tordex/trackball/main/paw3395/paw3395.cpp

#include "driver/spi_master.h"
#include "driver/gpio.h"
#include "driver/rtc_io.h"
#include <esp_private/esp_clk.h>
#include "esp_log.h"
#include "paw3395.h"

// Timing constants
const uint8_t PAW3395_TIMINGS_SRAD     = 2; // 2μs
const uint8_t PAW3395_TIMINGS_SRWSRR   = 2; // 2μs
const uint8_t PAW3395_TIMINGS_SWW      = 5; // 5μs
const uint8_t PAW3395_TIMINGS_SWR      = 5; // 5μs
const uint8_t PAW3395_TIMINGS_NCS_SCLK = 1; // 120ns
const uint8_t PAW3395_TIMINGS_BEXIT    = 4; // 500ns

const uint8_t PAW3395_SPI_WRITE = 0x80;

// Register addresses
const uint8_t PAW3395_REG_MOTION            = 0x02;
const uint8_t PAW3395_REG_DELTA_X_L         = 0x03;
const uint8_t PAW3395_REG_DELTA_X_H         = 0x04;
const uint8_t PAW3395_REG_DELTA_Y_L         = 0x05;
const uint8_t PAW3395_REG_DELTA_Y_H         = 0x06;
const uint8_t PAW3395_REG_MOTION_BURST      = 0x16;
const uint8_t PAW3395_REG_POWERUPRESET      = 0x3A;
const uint8_t PAW3395_REG_SET_RESOLUTION    = 0x47;
const uint8_t PAW3395_REG_RESOLUTION_X_LOW  = 0x48;
const uint8_t PAW3395_REG_RESOLUTION_X_HIGH = 0x49;
const uint8_t PAW3395_REG_RESOLUTION_Y_LOW  = 0x4A;
const uint8_t PAW3395_REG_RESOLUTION_Y_HIGH = 0x4B;
const uint8_t PAW3395_REG_RIPPLE_CONTROL    = 0x5A;
const uint8_t PAW3395_REG_MOTION_CTRL       = 0x5C;

// Register values
const uint8_t PAW3395_POWERUPRESET_POWERON = 0x5A;

// Register bits
const uint8_t PAW3395_OP_MODE0 = 0;
const uint8_t PAW3395_OP_MODE1 = 1;
const uint8_t PAW3395_PG_FIRST = 6;
const uint8_t PAW3395_PG_VALID = 7;

esp_err_t paw3395::init(spi_host_device_t host_id, gpio_num_t ncs_pin, gpio_num_t pin_motion,
                        const OnMotionCallback_t& on_motion)
{
    const uint8_t PAW3395_INVALID_PRODUCT_ID_0 = 0x00;
    const uint8_t PAW3395_INVALID_PRODUCT_ID_1 = 0xFF;
    const int     PAW3395_INIT_RETRIES         = 3;

    m_pin_ncs            = ncs_pin;
    m_pin_motion         = pin_motion;
    m_on_motion_callback = on_motion;

    // Configure NCS pin
    gpio_config_t io_conf = {};
    io_conf.pin_bit_mask  = (1ULL << m_pin_ncs);
    io_conf.mode          = GPIO_MODE_OUTPUT;
    io_conf.pull_up_en    = GPIO_PULLUP_DISABLE;
    io_conf.pull_down_en  = GPIO_PULLDOWN_DISABLE;
    io_conf.intr_type     = GPIO_INTR_DISABLE;
    gpio_config(&io_conf);

    cs_high();

    // Configure SPI device
    spi_device_interface_config_t devcfg = {};
    devcfg.clock_speed_hz                = 10000000; // 10MHz
    devcfg.mode                          = 3;        // SPI Mode 3 (CPOL=1, CPHA=1)
    devcfg.spics_io_num                  = -1;       // Manually control CS
    devcfg.queue_size                    = 7;

    esp_err_t ret = spi_bus_add_device(host_id, &devcfg, &m_spi);
    if(ret != ESP_OK)
    {
        ESP_LOGE(m_log_tag, "SPI device add failed: %d\n", ret);
        return ret;
    }

    cs_high();
    uint8_t product_id     = 0;
    uint8_t inv_product_id = 0;
    bool    init_ok        = false;
    for(int attempt = 1; attempt <= PAW3395_INIT_RETRIES; ++attempt)
    {
        Power_up_sequence();
        product_id     = read_register(0x00);
        inv_product_id = read_register(0x5F);

        if(product_id != PAW3395_INVALID_PRODUCT_ID_0 && product_id != PAW3395_INVALID_PRODUCT_ID_1 &&
           (product_id ^ inv_product_id) == 0xFF)
        {
            init_ok = true;
            break;
        }

        ESP_LOGW(m_log_tag, "Invalid Product ID 0x%02X/0x%02X (attempt %d/%d)", product_id, inv_product_id, attempt,
                 PAW3395_INIT_RETRIES);
        delay_ms(10);
    }

    if(!init_ok)
    {
        ESP_LOGE(m_log_tag, "PAW3395 init failed, invalid Product ID after retries: 0x%02X/0x%02X", product_id,
                 inv_product_id);
        return ESP_ERR_INVALID_RESPONSE;
    }

    ESP_LOGI(m_log_tag, "PAW3395 Product ID: 0x%02X", product_id);

    // Enable RIPPLE CONTROL
    write_register(PAW3395_REG_RIPPLE_CONTROL, 0x90);

    // Lift cut 2mm
    set_lift_cut(2);

    // Read and clear any pending motion data before starting normal operation.
    motion_burst_data data;
    for(int i = 0; i < 5; i++)
    {
        motion_burst(&data);
        vTaskDelay(pdMS_TO_TICKS(1));
    }

    ret = init_motion_pin();
    if(ret != ESP_OK)
    {
        ESP_LOGE(m_log_tag, "Failed to initialize motion pin");
        return ret;
    }

    // If MOTION is already low, no negedge will occur. Trigger one read cycle now.
    if(gpio_get_level(m_pin_motion) == 0)
    {
        ESP_LOGE(m_log_tag, "MOTION pin is already low");
    }

    if(xTaskCreate((TaskFunction_t) motion_task, "paw3395_motion", 4096, this, 5, &m_motion_task) != pdPASS)
    {
        ESP_LOGE(m_log_tag, "Failed to create motion task");
        return ESP_FAIL;
    }

    return ESP_OK;
}

void paw3395::set_lift_cut(uint8_t lift_height)
{
    write_register(0x7F, 0xC0);
    write_register(0x4E, lift_height);
    write_register(0x7F, 0x00);
}

static void IRAM_ATTR motion_isr_handler(void* arg)
{
    BaseType_t woken = pdFALSE;
    auto       sem   = static_cast<SemaphoreHandle_t>(arg);
    xSemaphoreGiveFromISR(sem, &woken);
    portYIELD_FROM_ISR(woken);
}

esp_err_t paw3395::init_motion_pin()
{
    if(!m_motion_semaphore)
    {
        m_motion_semaphore = xSemaphoreCreateBinary();
        if(!m_motion_semaphore)
        {
            ESP_LOGE(m_log_tag, "Failed to create semaphore");
            return ESP_FAIL;
        }
    }

    if(rtc_gpio_is_valid_gpio(m_pin_motion))
    {
        // When waking from deep sleep, wakeup pins can stay in RTC mode.
        // Release it so edge interrupts work in digital GPIO mode.
        rtc_gpio_deinit(m_pin_motion);
    }

    const gpio_config_t io_conf = {
        .pin_bit_mask = (1ULL << m_pin_motion),
        .mode         = GPIO_MODE_INPUT,
        .pull_up_en   = GPIO_PULLUP_ENABLE,
        .pull_down_en = GPIO_PULLDOWN_DISABLE,
        .intr_type    = GPIO_INTR_NEGEDGE,
    };
    esp_err_t ret = gpio_config(&io_conf);
    if(ret != ESP_OK)
    {
        ESP_LOGE(m_log_tag, "Motion pin gpio_config failed: %d", ret);
        return ret;
    }

    gpio_isr_handler_remove(m_pin_motion);

    ret = gpio_isr_handler_add(m_pin_motion, motion_isr_handler, m_motion_semaphore);
    if(ret != ESP_OK)
    {
        ESP_LOGE(m_log_tag, "gpio_isr_handler_add failed: %d", ret);
        return ret;
    }

    ret = gpio_intr_enable(m_pin_motion);
    if(ret != ESP_OK)
    {
        ESP_LOGE(m_log_tag, "gpio_intr_enable failed: %d", ret);
        return ret;
    }

    return ESP_OK;
}

void paw3395::stop_motion_task()
{
    m_stop = true;
    vTaskDelay(pdMS_TO_TICKS(7)); // Give some time for the motion task to exit
    gpio_intr_disable(m_pin_motion);
    gpio_isr_handler_remove(m_pin_motion);
}

void paw3395::motion_task(void* param)
{
    auto pThis = static_cast<paw3395*>(param);
    while(!pThis->m_stop)
    {
        if(pThis->m_motion_semaphore && xSemaphoreTake(pThis->m_motion_semaphore, pdMS_TO_TICKS(5)))
        {
            int16_t dx      = 0;
            int16_t dy      = 0;
            int     counter = 0;
            while(counter < 5)
            {
                if(pThis->read_motion_burst(&dx, &dy))
                {
                    if(pThis->m_on_motion_callback)
                    {
                        pThis->m_on_motion_callback(dx, dy);
                    }
                } else
                {
                    counter++;
                    vTaskDelay(pdMS_TO_TICKS(1));
                }
            }
        }
    }
    vTaskDelete(NULL);
}

void paw3395::delay_125_ns(uint8_t nns)
{
    uint32_t cpu_freq_hz = esp_clk_cpu_freq();
    uint32_t cycles      = (125 * nns) / (1000000000 / cpu_freq_hz);
    uint32_t start       = esp_cpu_get_cycle_count();
    while(esp_cpu_get_cycle_count() - start < cycles)
        ;
}

uint8_t paw3395::SPI_SendReceive(uint8_t data)
{
    spi_transaction_t t = {};
    t.length            = 8;
    t.tx_buffer         = &data;
    t.rxlength          = 8;
    t.rx_buffer         = &data;

    esp_err_t ret = spi_device_polling_transmit(m_spi, &t);
    if(ret != ESP_OK)
    {
        printf("SPI transaction failed: %d\n", ret);
    }
    return data;
}

uint8_t paw3395::read_register(uint8_t address, bool apply_cs)
{
    if(apply_cs)
    {
        cs_low();
    }
    delay_125_ns(1);
    SPI_SendReceive(address);
    delay_us(5); // t_SRAD
    uint8_t temp = SPI_SendReceive(0xFF);
    if(apply_cs)
    {
        cs_high();
    }
    delay_us(5); // t_SWW
    return temp;
}

void paw3395::write_register(uint8_t address, uint8_t value)
{
    cs_low();
    delay_125_ns(1);
    SPI_SendReceive(address | 0x80);
    SPI_SendReceive(value);
    cs_high();
    delay_us(5); // t_SWW
}

void paw3395::Power_up_sequence()
{
    uint8_t reg_it;
    delay_ms(60);
    cs_low();
    delay_125_ns(PAW3395_TIMINGS_NCS_SCLK);
    cs_high();
    delay_125_ns(PAW3395_TIMINGS_NCS_SCLK);
    cs_low();
    delay_125_ns(PAW3395_TIMINGS_NCS_SCLK);

    write_register(PAW3395_REG_POWERUPRESET, PAW3395_POWERUPRESET_POWERON);
    delay_ms(10);
    Power_Up_Initializaton_Register_Setting();
    cs_high();
    delay_125_ns(PAW3395_TIMINGS_NCS_SCLK);

    for(reg_it = 0x02; reg_it <= 0x06; reg_it++)
    {
        read_register(reg_it);
        delay_us(PAW3395_TIMINGS_SRWSRR);
    }
    cs_high();
    delay_125_ns(PAW3395_TIMINGS_BEXIT);
}

bool paw3395::read_motion(int16_t* dx, int16_t* dy)
{
    uint8_t motion, x_l, x_h, y_l, y_h;

    // Read the Motion register. This will freeze the Delta_X and Delta_Y registers until they are read.
    motion = read_register(PAW3395_REG_MOTION);
    if((motion & 0x80) != 0)
    {
        cs_low();
        x_l = read_register(PAW3395_REG_DELTA_X_L, false);
        x_h = read_register(PAW3395_REG_DELTA_X_H, false);
        y_l = read_register(PAW3395_REG_DELTA_Y_L, false);
        y_h = read_register(PAW3395_REG_DELTA_Y_H, false);
        cs_high();

        *dx = (int16_t) (x_l | (x_h << 8));
        *dy = (int16_t) (y_l | (y_h << 8));
        return *dx != 0 || *dy != 0;
    }
    *dx = 0;
    *dy = 0;
    return false;
}

bool paw3395::read_motion_burst(int16_t* dx, int16_t* dy)
{
    motion_burst_data burst = {};
    motion_burst(&burst);
    if((burst.motion & 0x80) != 0)
    {
        *dx = (int16_t) (burst.delta_x_l | (burst.delta_x_h << 8));
        *dy = (int16_t) (burst.delta_y_l | (burst.delta_y_h << 8));
        return *dx != 0 || *dy != 0;
    }
    *dx = 0;
    *dy = 0;
    return false;
}

void paw3395::motion_burst(motion_burst_data* values)
{
    uint8_t* buffer = reinterpret_cast<uint8_t*>(values);
    cs_low();
    delay_125_ns(PAW3395_TIMINGS_NCS_SCLK);
    SPI_SendReceive(PAW3395_REG_MOTION_BURST);
    delay_us(PAW3395_TIMINGS_SRAD);
    for(uint8_t i = 0; i < 12; i++)
    {
        buffer[i] = SPI_SendReceive(0x00);
    }
    cs_high();
    delay_125_ns(PAW3395_TIMINGS_BEXIT);
}

void paw3395::Power_Up_Initializaton_Register_Setting()
{
    uint8_t read_tmp;
    uint8_t i;
    write_register(0x7F, 0x07);
    write_register(0x40, 0x41);
    write_register(0x7F, 0x00);
    write_register(0x40, 0x80);
    write_register(0x7F, 0x0E);
    write_register(0x55, 0x0D);
    write_register(0x56, 0x1B);
    write_register(0x57, 0xE8);
    write_register(0x58, 0xD5);
    write_register(0x7F, 0x14);
    write_register(0x42, 0xBC);
    write_register(0x43, 0x74);
    write_register(0x4B, 0x20);
    write_register(0x4D, 0x00);
    write_register(0x53, 0x0E);
    write_register(0x7F, 0x05);
    write_register(0x44, 0x04);
    write_register(0x4D, 0x06);
    write_register(0x51, 0x40);
    write_register(0x53, 0x40);
    write_register(0x55, 0xCA);
    write_register(0x5A, 0xE8);
    write_register(0x5B, 0xEA);
    write_register(0x61, 0x31);
    write_register(0x62, 0x64);
    write_register(0x6D, 0xB8);
    write_register(0x6E, 0x0F);

    write_register(0x70, 0x02);
    write_register(0x4A, 0x2A);
    write_register(0x60, 0x26);
    write_register(0x7F, 0x06);
    write_register(0x6D, 0x70);
    write_register(0x6E, 0x60);
    write_register(0x6F, 0x04);
    write_register(0x53, 0x02);
    write_register(0x55, 0x11);
    write_register(0x7A, 0x01);
    write_register(0x7D, 0x51);
    write_register(0x7F, 0x07);
    write_register(0x41, 0x10);
    write_register(0x42, 0x32);
    write_register(0x43, 0x00);
    write_register(0x7F, 0x08);
    write_register(0x71, 0x4F);
    write_register(0x7F, 0x09);
    write_register(0x62, 0x1F);
    write_register(0x63, 0x1F);
    write_register(0x65, 0x03);
    write_register(0x66, 0x03);
    write_register(0x67, 0x1F);
    write_register(0x68, 0x1F);
    write_register(0x69, 0x03);
    write_register(0x6A, 0x03);
    write_register(0x6C, 0x1F);

    write_register(0x6D, 0x1F);
    write_register(0x51, 0x04);
    write_register(0x53, 0x20);
    write_register(0x54, 0x20);
    write_register(0x71, 0x0C);
    write_register(0x72, 0x07);
    write_register(0x73, 0x07);
    write_register(0x7F, 0x0A);
    write_register(0x4A, 0x14);
    write_register(0x4C, 0x14);
    write_register(0x55, 0x19);
    write_register(0x7F, 0x14);
    write_register(0x4B, 0x30);
    write_register(0x4C, 0x03);
    write_register(0x61, 0x0B);
    write_register(0x62, 0x0A);
    write_register(0x63, 0x02);
    write_register(0x7F, 0x15);
    write_register(0x4C, 0x02);
    write_register(0x56, 0x02);
    write_register(0x41, 0x91);
    write_register(0x4D, 0x0A);
    write_register(0x7F, 0x0C);
    write_register(0x4A, 0x10);
    write_register(0x4B, 0x0C);
    write_register(0x4C, 0x40);
    write_register(0x41, 0x25);
    write_register(0x55, 0x18);
    write_register(0x56, 0x14);
    write_register(0x49, 0x0A);
    write_register(0x42, 0x00);
    write_register(0x43, 0x2D);
    write_register(0x44, 0x0C);
    write_register(0x54, 0x1A);
    write_register(0x5A, 0x0D);
    write_register(0x5F, 0x1E);
    write_register(0x5B, 0x05);
    write_register(0x5E, 0x0F);
    write_register(0x7F, 0x0D);
    write_register(0x48, 0xDD);
    write_register(0x4F, 0x03);
    write_register(0x52, 0x49);

    write_register(0x51, 0x00);
    write_register(0x54, 0x5B);
    write_register(0x53, 0x00);

    write_register(0x56, 0x64);
    write_register(0x55, 0x00);
    write_register(0x58, 0xA5);
    write_register(0x57, 0x02);
    write_register(0x5A, 0x29);
    write_register(0x5B, 0x47);
    write_register(0x5C, 0x81);
    write_register(0x5D, 0x40);
    write_register(0x71, 0xDC);
    write_register(0x70, 0x07);
    write_register(0x73, 0x00);
    write_register(0x72, 0x08);
    write_register(0x75, 0xDC);
    write_register(0x74, 0x07);
    write_register(0x77, 0x00);
    write_register(0x76, 0x08);
    write_register(0x7F, 0x10);
    write_register(0x4C, 0xD0);
    write_register(0x7F, 0x00);
    write_register(0x4F, 0x63);
    write_register(0x4E, 0x00);
    write_register(0x52, 0x63);
    write_register(0x51, 0x00);
    write_register(0x54, 0x54);
    write_register(0x5A, 0x10);
    write_register(0x77, 0x4F);
    write_register(0x47, 0x01);
    write_register(0x5B, 0x40);
    write_register(0x64, 0x60);
    write_register(0x65, 0x06);
    write_register(0x66, 0x13);
    write_register(0x67, 0x0F);
    write_register(0x78, 0x01);
    write_register(0x79, 0x9C);
    write_register(0x40, 0x00);
    write_register(0x55, 0x02);
    write_register(0x23, 0x70);
    write_register(0x22, 0x01);

    delay_ms(1);

    for(i = 0; i < 60; i++)
    {
        read_tmp = read_register(0x6C);
        if(read_tmp == 0x80)
        {
            break;
        }
        delay_ms(1);
    }
    if(i == 60)
    {
        write_register(0x7F, 0x14);
        write_register(0x6C, 0x00);
        write_register(0x7F, 0x00);
    }
    write_register(0x22, 0x00);
    write_register(0x55, 0x00);
    write_register(0x7F, 0x07);
    write_register(0x40, 0x40);
    write_register(0x7F, 0x00);
}

void paw3395::set_dpi(uint16_t CPI_Num)
{
    uint8_t temp;
    write_register(PAW3395_REG_MOTION_CTRL, 0x00);
    temp = (uint8_t) (((CPI_Num / 50) << 8) >> 8);
    write_register(PAW3395_REG_RESOLUTION_X_LOW, temp);
    temp = (uint8_t) ((CPI_Num / 50) >> 8);
    write_register(PAW3395_REG_RESOLUTION_X_HIGH, temp);
    write_register(PAW3395_REG_SET_RESOLUTION, 0x01);
}

void paw3395::office_mode()
{
    write_register(0x7F, 0x05);
    write_register(0x51, 0x28);
    write_register(0x53, 0x30);
    write_register(0x61, 0x3B);
    write_register(0x6E, 0x1F);
    write_register(0x7F, 0x07);
    write_register(0x42, 0x32);
    write_register(0x43, 0x00);
    write_register(0x7F, 0x0D);
    write_register(0x51, 0x00);
    write_register(0x52, 0x49);
    write_register(0x53, 0x00);
    write_register(0x54, 0x5B);
    write_register(0x55, 0x00);
    write_register(0x56, 0x64);
    write_register(0x57, 0x02);
    write_register(0x58, 0xA5);
    write_register(0x7F, 0x00);
    write_register(0x54, 0x52);
    write_register(0x78, 0x0A);
    write_register(0x79, 0x0F);
    uint8_t tmp = read_register(0x40);
    tmp         = (tmp & 0xFC) | 0x02;
    write_register(0x40, tmp);
}

void paw3395::gaming_mode()
{
    write_register(0x7F, 0x05);
    write_register(0x51, 0x40);
    write_register(0x53, 0x40);
    write_register(0x61, 0x31);
    write_register(0x6E, 0x0F);
    write_register(0x7F, 0x07);
    write_register(0x42, 0x2F);
    write_register(0x43, 0x00);
    write_register(0x7F, 0x0D);
    write_register(0x51, 0x12);
    write_register(0x52, 0xDB);
    write_register(0x53, 0x12);
    write_register(0x54, 0xDC);
    write_register(0x55, 0x12);
    write_register(0x56, 0xEA);
    write_register(0x57, 0x15);
    write_register(0x58, 0x2D);
    write_register(0x7F, 0x00);
    write_register(0x54, 0x55);
    write_register(0x40, 0x83);
}

void paw3395::low_power_mode()
{
    write_register(0x7F, 0x05);
    write_register(0x51, 0x40);
    write_register(0x53, 0x40);
    write_register(0x61, 0x3B);
    write_register(0x6E, 0x1F);
    write_register(0x7F, 0x07);
    write_register(0x42, 0x32);
    write_register(0x43, 0x00);
    write_register(0x7F, 0x0D);
    write_register(0x51, 0x00);
    write_register(0x52, 0x49);
    write_register(0x53, 0x00);
    write_register(0x54, 0x5B);
    write_register(0x55, 0x00);
    write_register(0x56, 0x64);
    write_register(0x57, 0x02);
    write_register(0x58, 0xA5);
    write_register(0x7F, 0x00);
    write_register(0x54, 0x54);
    write_register(0x78, 0x01);
    write_register(0x79, 0x9C);
    uint8_t tmp = read_register(0x40);
    tmp         = (tmp & 0xFC) | 0x01;
    write_register(0x40, tmp);
}

void paw3395::high_performance_mode()
{
    write_register(0x7F, 0x05);
    write_register(0x51, 0x40);
    write_register(0x53, 0x40);
    write_register(0x61, 0x31);
    write_register(0x6E, 0x0F);
    write_register(0x7F, 0x07);
    write_register(0x42, 0x32);
    write_register(0x43, 0x00);
    write_register(0x7F, 0x0D);
    write_register(0x51, 0x00);
    write_register(0x52, 0x49);
    write_register(0x53, 0x00);
    write_register(0x54, 0x5B);
    write_register(0x55, 0x00);
    write_register(0x56, 0x64);
    write_register(0x57, 0x02);
    write_register(0x58, 0xA5);
    write_register(0x7F, 0x00);
    write_register(0x54, 0x54);
    write_register(0x78, 0x01);
    write_register(0x79, 0x9C);
    uint8_t tmp = read_register(0x40);
    tmp         = (tmp & 0xFC) | 0x00;
    write_register(0x40, tmp);
}
