tordex/trackball/main/types.h

#ifndef __TYPES_H__
#define __TYPES_H__

#include <cstdint>

const uint8_t SCROLL_MODE_HIGH_RES       = 0x01;
const uint8_t SCROLL_MODE_ENABLE_HSCROLL = 0x02;
const uint8_t SCROLL_MODE_ENABLE_VSCROLL = 0x04;

#endif // __TYPES_H__
