tordex/trackball/main/ui.cpp

#include "ui.h"
#include <cstring>
#include <cstdio>
#include <vector>
#include <string>

// Include bitmap definitions
#include "images/images.c"
#include <esp_private/esp_clk.h>

trackball_ui::~trackball_ui()
{
    deinit();
}

void trackball_ui::init(i2c_master_dev_handle_t oled_dev)
{
    ssd1306_init(&m_oled_data, 128, 64, oled_dev);
    ssd1306_poweron(&m_oled_data);
    ssd1306_clear(&m_oled_data);
    ssd1306_show(&m_oled_data);
    draw_status_line();
    draw_ui_state();
    ssd1306_show(&m_oled_data);
}

void trackball_ui::power_off()
{
    ssd1306_poweroff(&m_oled_data);
}

void trackball_ui::power_on()
{
    ssd1306_poweron(&m_oled_data);
}

void trackball_ui::deinit()
{
    ssd1306_deinit(&m_oled_data);
}

void trackball_ui::set_connection_state(bool connected, int8_t rssi, bool rssi_valid)
{
    if(m_connected == connected && m_rssi == rssi && m_rssi_valid == rssi_valid)
    {
        return;
    }

    m_connected  = connected;
    m_rssi       = rssi;
    m_rssi_valid = rssi_valid;
    draw_status_line();
    ssd1306_show(&m_oled_data);
}

void trackball_ui::set_ui_state(ui_state_t state)
{
    if(m_ui_state != state)
    {
        m_ui_state = state;
        draw_status_line();
        draw_ui_state();
    }
}

void trackball_ui::set_battery_level(int bat_mV, int level)
{
    bool show = false;
    if(m_bat_mV != bat_mV)
    {
        m_bat_mV = bat_mV;
        if(m_ui_state == UI_STATE_DEFAULT)
        {
            draw_ui_default();
            show = true;
        }
    }
    if(m_bat_level != level)
    {
        m_bat_level = level;
        if(m_ui_state == UI_STATE_DEFAULT)
        {
            draw_status_line();
            show = true;
        }
    }
    if(show)
    {
        ssd1306_show(&m_oled_data);
    }
}

void trackball_ui::start_menu(ui_menu::submenu* menu)
{
    m_current_menu = menu;
    m_ui_state     = UI_STATE_MENU;
    draw_ui_menu();
    ssd1306_show(&m_oled_data);
}

void trackball_ui::on_scroll(int16_t wheel)
{
    if(m_ui_state != UI_STATE_MENU || !m_current_menu)
    {
        return;
    }
    int step = 0;
    if(wheel > 0)
    {
        step = 1;
    } else if(wheel < 0)
    {
        step = -1;
    }
    if(step)
    {
        if(m_current_menu->on_scroll(step))
        {
            draw_ui_menu();
            ssd1306_show(&m_oled_data);
        }
    }
}

void trackball_ui::on_menu_confirm()
{
    if(!m_current_menu)
    {
        return;
    }
    m_current_menu->on_confirm(true);
    draw_ui_menu();
    ssd1306_show(&m_oled_data);
}

bool trackball_ui::on_menu_back()
{
    if(!m_current_menu)
    {
        return false;
    }
    auto ret = m_current_menu->on_back();
    draw_ui_menu();
    ssd1306_show(&m_oled_data);
    return ret;
}

void trackball_ui::draw_status_line()
{
    if(m_ui_state == UI_STATE_GO_SLEEP || m_ui_state == UI_STATE_MENU)
    {
        return;
    }

    ssd1306_clear_square(&m_oled_data, 0, 0, 128, 15);
    if(m_connected)
    {
        if(m_rssi_valid)
        {
            if(m_rssi > -55)
            {
                ssd1306_bmp_show_image_with_offset(&m_oled_data, signal_4of4_bmp, signal_4of4_bmp_len, 0, 0);
            } else if(m_rssi > -65)
            {
                ssd1306_bmp_show_image_with_offset(&m_oled_data, signal_3of4_bmp, signal_3of4_bmp_len, 0, 0);
            } else if(m_rssi > -70)
            {
                ssd1306_bmp_show_image_with_offset(&m_oled_data, signal_2of4_bmp, signal_2of4_bmp_len, 0, 0);
            } else
            {
                ssd1306_bmp_show_image_with_offset(&m_oled_data, signal_1of4_bmp, signal_1of4_bmp_len, 0, 0);
            }
            // Draw RSSI if valid
            char level_str[20] = {};
            snprintf(level_str, sizeof(level_str), "%ddBm", m_rssi);
            ssd1306_draw_string(&m_oled_data, 17, 2, 1, level_str);
        } else
        {
            ssd1306_bmp_show_image_with_offset(&m_oled_data, signal_disconnected_bmp, signal_disconnected_bmp_len, 0,
                                               0);
        }
    } else
    {
        ssd1306_bmp_show_image_with_offset(&m_oled_data, signal_disconnected_bmp, signal_disconnected_bmp_len, 0, 0);
    }

    struct
    {
        unsigned char* bmp;
        size_t         len;
    } levels[] = {
        {battery_0of6_bmp, battery_0of6_bmp_len},
        {battery_1of6_bmp, battery_1of6_bmp_len},
        {battery_2of6_bmp, battery_2of6_bmp_len},
        {battery_3of6_bmp, battery_3of6_bmp_len},
        {battery_4of6_bmp, battery_4of6_bmp_len},
        {battery_5of6_bmp, battery_5of6_bmp_len},
        {battery_6of6_bmp, battery_6of6_bmp_len},
    };
    float idx_f = (float) m_bat_level * 7.0f / 100.0f;
    int   idx   = (int) (idx_f);
    if(idx_f - idx >= 0.5f)
    {
        idx++;
    }
    if(idx < 0)
    {
        idx = 0;
    }
    if(idx > 6)
    {
        idx = 6;
    }
    ssd1306_bmp_show_image_with_offset(&m_oled_data, levels[idx].bmp, levels[idx].len, 111, 0);

    // Draw battery percentage
    char bat_str[10] = {};
    snprintf(bat_str, sizeof(bat_str), " %3d%%", m_bat_level);
    ssd1306_draw_string(&m_oled_data, 80, 2, 1, bat_str);

    // Draw separator line
    ssd1306_draw_line(&m_oled_data, 0, 13, 128, 13);
}

void trackball_ui::draw_ui_state()
{
    switch(m_ui_state)
    {
    case UI_STATE_DEFAULT:
        draw_ui_default();
        break;
    case UI_STATE_SCROLL_LOCK:
        draw_ui_scroll_lock();
        break;
    case UI_STATE_LOCK_BUTTONS:
        draw_ui_lock_buttons();
        break;
    case UI_STATE_GO_SLEEP:
        draw_ui_go_sleep();
        break;
    case UI_STATE_MENU:
        draw_ui_menu();
        break;
    default:
        break;
    }
    ssd1306_show(&m_oled_data);
}

void trackball_ui::draw_ui_default()
{
    ssd1306_clear_square(&m_oled_data, 0, 16, 128, 48);

    char str_draw[30] = {};
    snprintf(str_draw, sizeof(str_draw), "BAT:%.3fV", m_bat_mV / 1000.0f);
    ssd1306_draw_string(&m_oled_data, 0, 16, 2, str_draw);

    strcpy(str_draw, "SCL:");
    if(m_scroll_mode & SCROLL_MODE_HIGH_RES)
    {
        strcat(str_draw, "HR ");
    }
    if(m_scroll_mode & SCROLL_MODE_ENABLE_VSCROLL)
    {
        strcat(str_draw, "V ");
    }
    if(m_scroll_mode & SCROLL_MODE_ENABLE_HSCROLL)
    {
        strcat(str_draw, "H ");
    }
    ssd1306_draw_string(&m_oled_data, 0, 32, 2, str_draw);

    snprintf(str_draw, sizeof(str_draw), "DPI:%d", m_dpi);
    ssd1306_draw_string(&m_oled_data, 0, 48, 2, str_draw);
}

void trackball_ui::draw_ui_scroll_lock()
{
    ssd1306_clear_square(&m_oled_data, 0, 16, 128, 48);
    ssd1306_bmp_show_image_with_offset(&m_oled_data, scroll_lock_bmp, scroll_lock_bmp_len, 46, 16);

    int y = 16;
    if(m_scroll_mode & SCROLL_MODE_HIGH_RES)
    {
        ssd1306_draw_string(&m_oled_data, 0, y, 2, "HR");
        y += 16;
    }
    if(m_scroll_mode & SCROLL_MODE_ENABLE_VSCROLL)
    {
        ssd1306_draw_string(&m_oled_data, 0, y, 2, "V");
        y += 16;
    }
    if(m_scroll_mode & SCROLL_MODE_ENABLE_HSCROLL)
    {
        ssd1306_draw_string(&m_oled_data, 0, y, 2, "H");
        y += 16;
    }
}

void trackball_ui::draw_ui_lock_buttons()
{
    ssd1306_clear_square(&m_oled_data, 0, 16, 128, 48);
    ssd1306_bmp_show_image_with_offset(&m_oled_data, lock_buttons_bmp, lock_buttons_bmp_len, 92, 16);
    int         idx = 0;
    const char* strs[3];
    if(m_locked_buttons & 0x01)
    {
        strs[idx++] = "LEFT";
    }
    if(m_locked_buttons & 0x02)
    {
        strs[idx++] = "RIGHT";
    }
    if(m_locked_buttons & 0x04)
    {
        strs[idx++] = "MIDDLE";
    }
    int top = 16 + 48 / 2 - idx * 16 / 2;
    for(int i = 0; i < idx; i++)
    {
        ssd1306_draw_string(&m_oled_data, 0, top + i * 16, 2, strs[i]);
    }
}

void trackball_ui::draw_ui_go_sleep()
{
    ssd1306_clear(&m_oled_data);
    ssd1306_draw_string(&m_oled_data, 0, 32, 2, "GO SLEEP");
}

void trackball_ui::draw_ui_menu()
{
    if(!m_current_menu)
    {
        return;
    }
    m_current_menu->on_draw_focused(&m_oled_data, 0, 0);
}
